SP5GW/Crystal_Radio_Receiver/img/ReceiverPhotos/IMG_1018_radio_internal.jpg

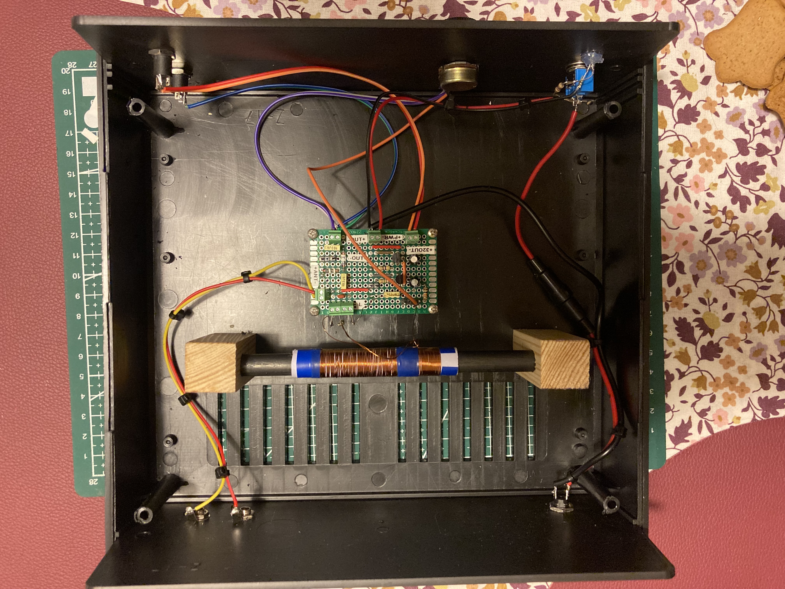
img/ReceiverPhotos/IMG_1018_radio_internal.jpg
