SP5GW/Crystal_Radio_Receiver/img/SolecKujawskiSite/SolecKujawski_2.jpg

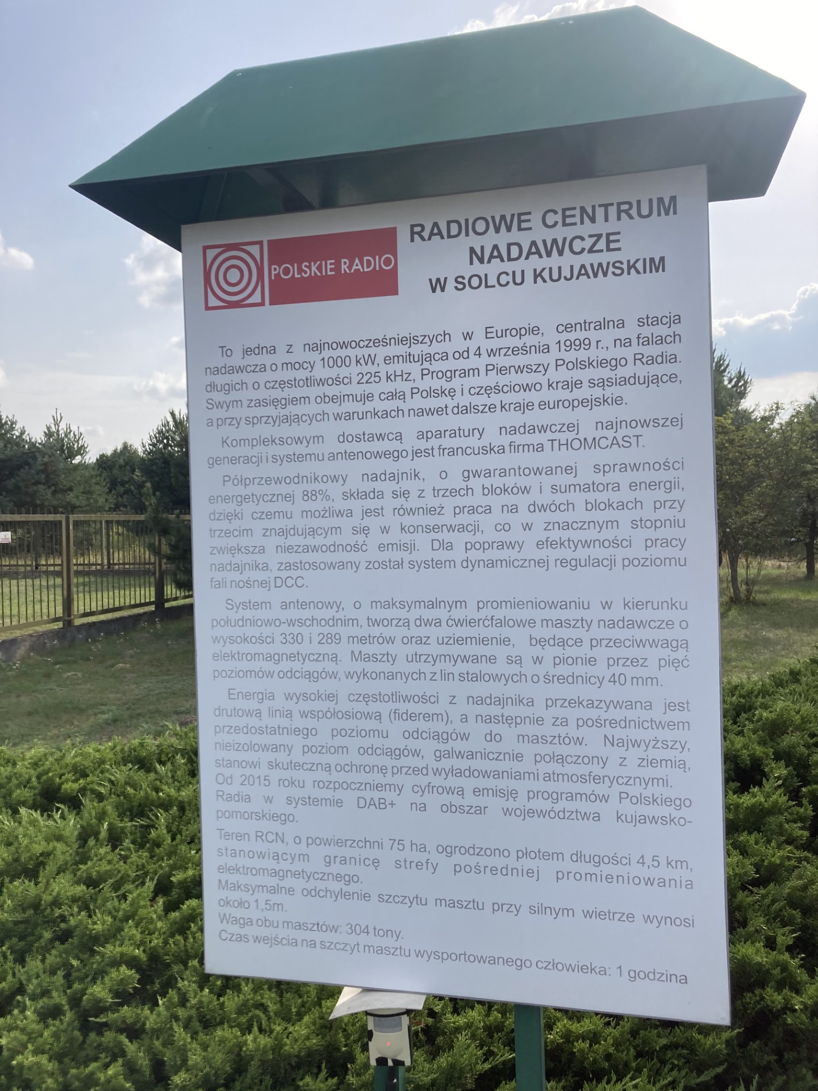
img/SolecKujawskiSite/SolecKujawski_2.jpg
