SP5GW/Crystal_Radio_Receiver/meas/power_supply_filter/0_Unfiltered_signal.png

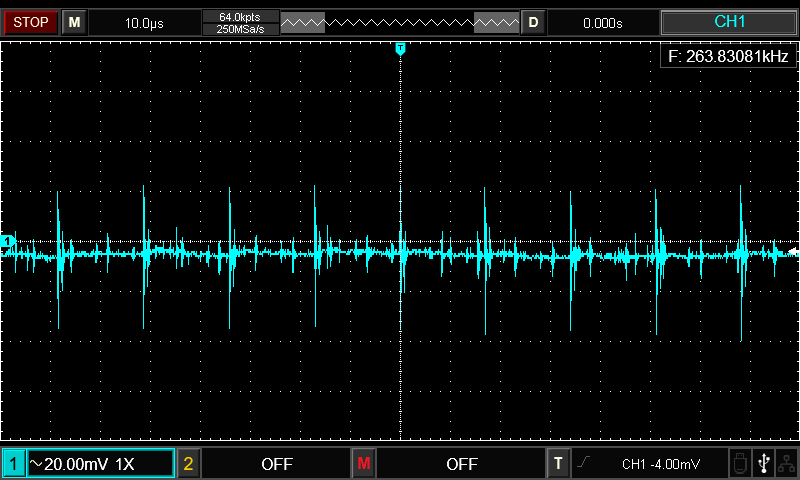
meas/power_supply_filter/0_Unfiltered_signal.png
