SP5GW/Crystal_Radio_Receiver/meas/power_supply_filter/1_C1_cap_added.png

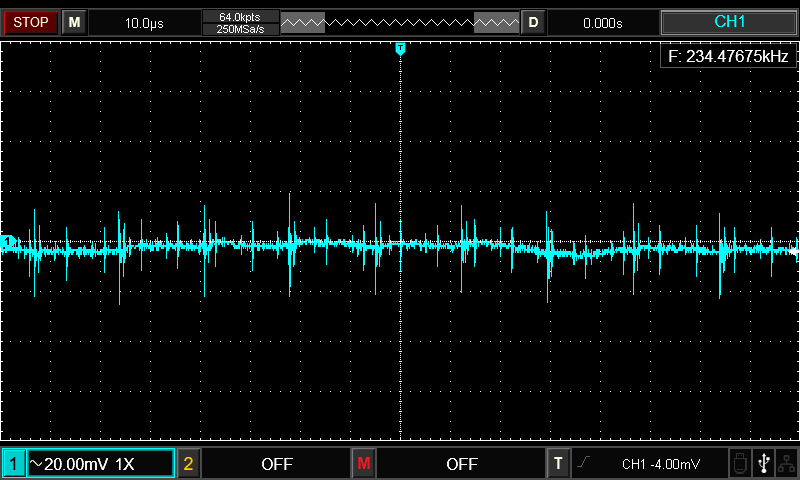
meas/power_supply_filter/1_C1_cap_added.png
