SP5GW/Crystal_Radio_Receiver/meas/power_supply_filter/2__C1_cap_and_L1_added.png

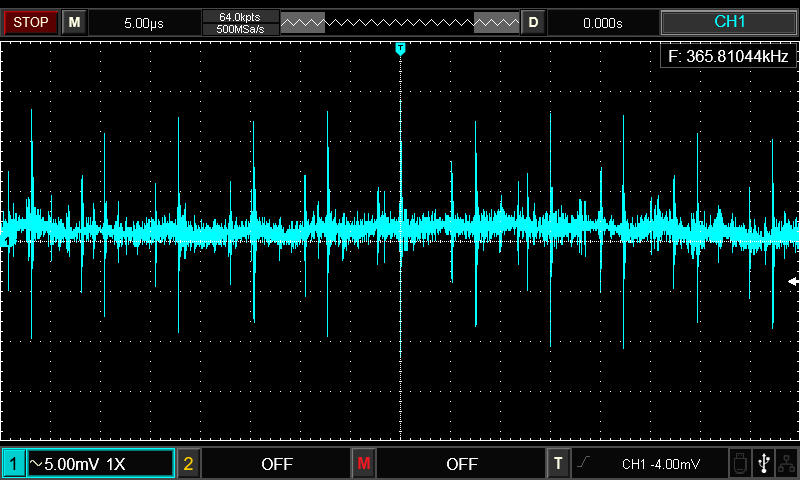
meas/power_supply_filter/2__C1_cap_and_L1_added.png
