SP5GW/Crystal_Radio_Receiver/meas/power_supply_filter/5__C1_cap_and_L1_C2_C3_L2_reg_added.png

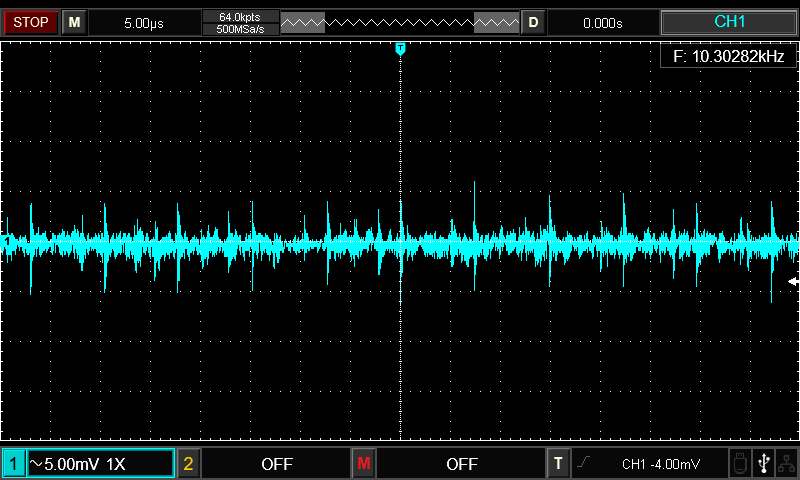
meas/power_supply_filter/5__C1_cap_and_L1_C2_C3_L2_reg_added.png
