SP5GW/Crystal_Radio_Receiver/sim/BandpassFilterStage_Circuit_Ant_Res.png

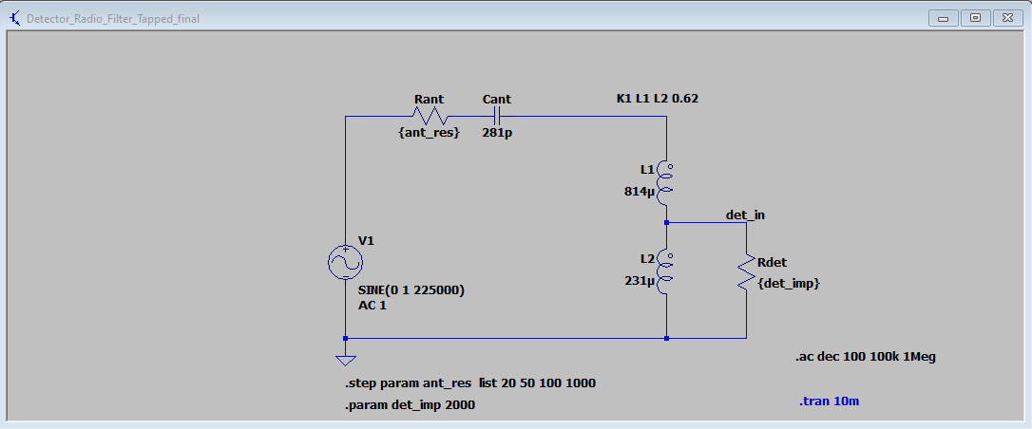
sim/BandpassFilterStage_Circuit_Ant_Res.png
