SP5GW/Crystal_Radio_Receiver/sim/BandpassFilterStage_Circuit_Cap_Add.png

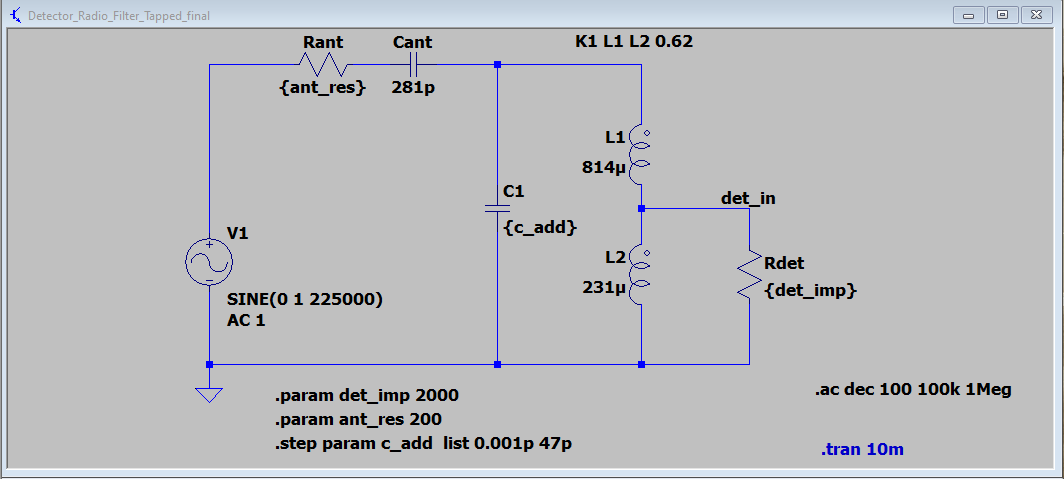
sim/BandpassFilterStage_Circuit_Cap_Add.png
