SP5GW/Crystal_Radio_Receiver/sim/BandpassFilterStage_Circuit_Det_Res.png

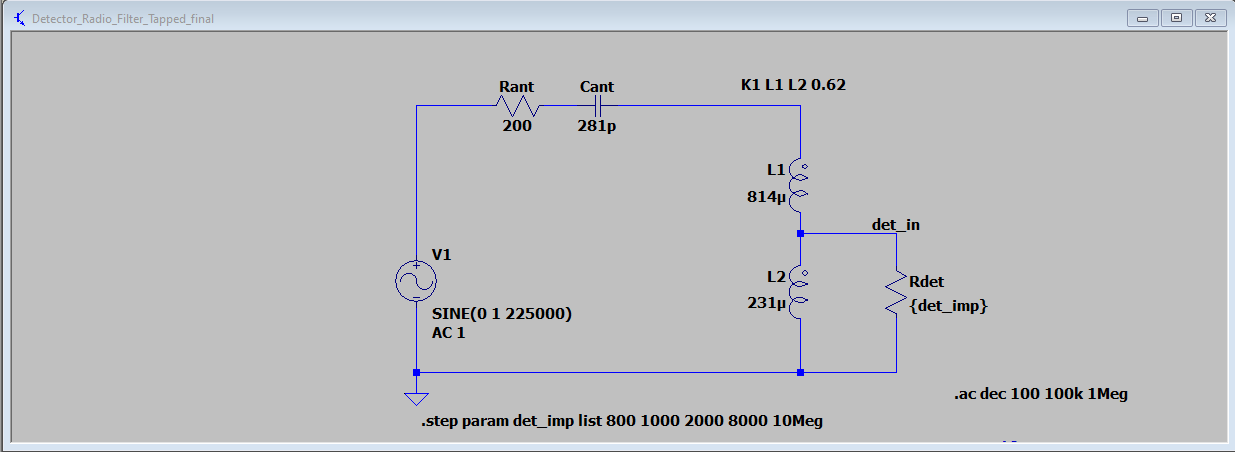
sim/BandpassFilterStage_Circuit_Det_Res.png
