SP5GW/Crystal_Radio_Receiver/sim/BandpassFilterStage_FrequencyResponse_Cap_Add.png

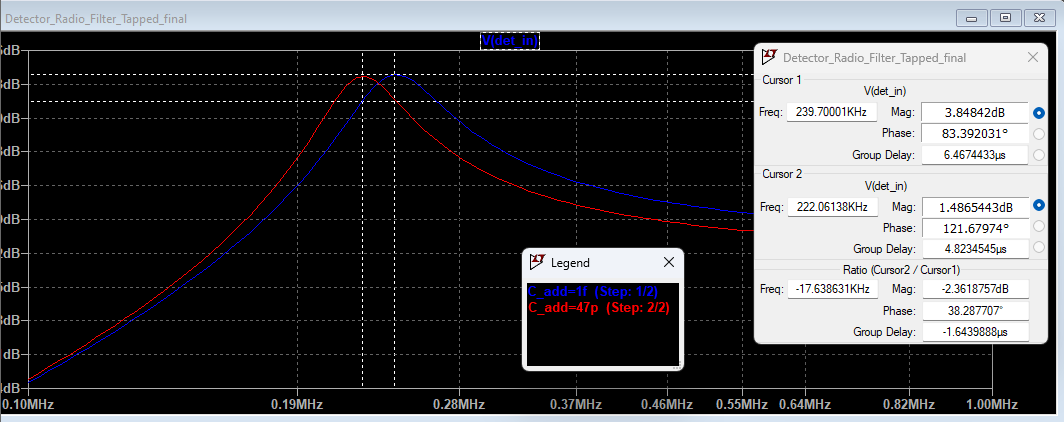
sim/BandpassFilterStage_FrequencyResponse_Cap_Add.png
