SP5GW/Crystal_Radio_Receiver/sim/BandpassFilterStage_FrequencyResponse_Det_Res.png

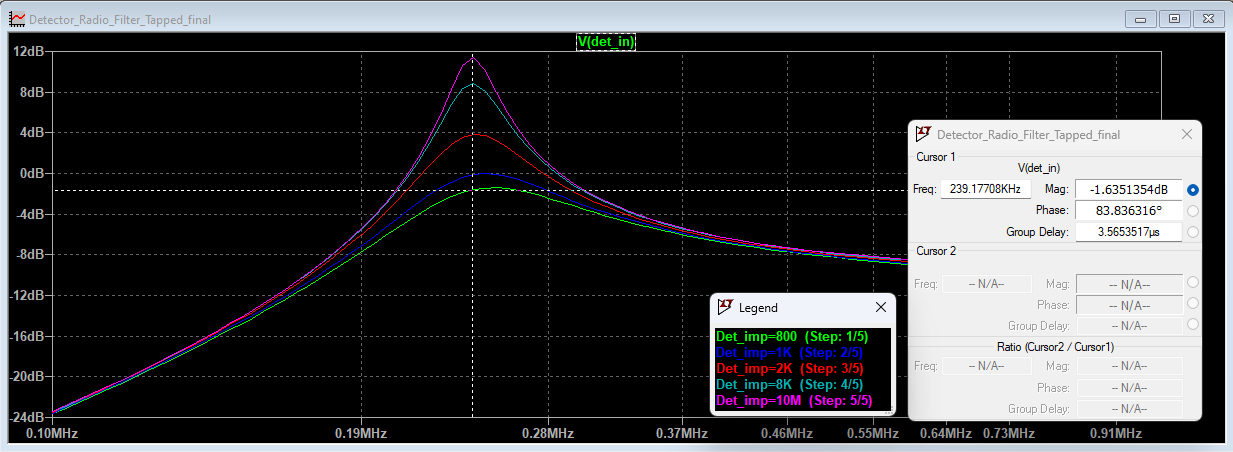
sim/BandpassFilterStage_FrequencyResponse_Det_Res.png
