SP5GW/Crystal_Radio_Receiver/sim/Detector_Radio_Complete_final.asc

B1: bv; V=V(Carrier)*V(Baseband)
C1: cap; 10n
C2: cap; 10n
C3: cap; 47p
C4: cap; 10µ
C5: polcap; 10µ; V=16 Irms=413m Rser=0.22 Lser=0 mfg="Chemi-Con" pn="LXF16VB181M6X15LL" type="Al electrolytic"
C6: cap; 10n
Cant: cap; 281p
D1: schottky; 1N34A
D2: schottky; 1N34A
L1: ind2; 231µ
L2: ind2; 814µ
Pot1: res; 150k
Pot2: res; 50k
Q1: npn; BC547B
Q2: pnp; BC557B
R2: res; 6.8Meg
R3: res; 47
R4: res; 4000
R5: res; 10k
Rantsysloss: res; 200
V1: signal; SINE(0 1 225K)
V2: signal; SINE(0.1 0.08 1K)
V4: voltage; 12V
Named nets: 0, Carrier, Baseband, LCout, DetOut, AmpOut, AntOut
.ac dec 100 100k 1Meg
.tran 10m
K L1 L2 0.61
