SP5GW/Crystal_Radio_Receiver/sim/Detector_Radio_Filter_Tapped_final.asc

C1: cap; {c_add}
Cant: cap; 281p
L1: ind2; 814µ
L1_a: ind2; 814
L2: ind2; 231µ
L2_a: ind2; 231
L3: ind2; 231
L4: ind2; 814
Leff: ind2; 1.583
R1: res; 20
R2: res; 20
R3: res; 20
R4: res; 2000
R_load: res; 2000
Rant: res; {ant_res}
Rdet: res; {det_imp}
Rdet_b: res; 13705
Rload_: res; 13705
V1: signal; SINE(0 1 225000); AC 1
V2: signal; SINE(0 1 225000); AC 1
V3: signal; SINE(0 1 225000); AC 1
V4: signal; SINE(0 1 225000); AC 1
Named nets: 0, det_in, det_in_b
.ac dec 100 100k 1Meg
.tran 10m
K1 L1 L2 0.62
.step param det_imp list 800 1000 2000 8000 10Meg
K2 L1_a L2_a 0.62
.param det_imp 2000
Base Circuit
Variant a) using idealized transformer with massive reactances
< === equivalent ===>
k=M/SQRT(L1*L2) => M=k/SQRT(L1*L2)
M=0.62*SQRT(814*231*10^-12)=269uH
 
Lp = L1+L2+2M
Lp=814u+231u+2*269u=1583u
 
fr=1/(2*PI*SQRT(Lp*Cant)
fr=1/(2*3.14*SQRT(1583*281*10^-18))=239kHz
Ls=L2
Ls=231u
 
Lp=1583u
 
N=(Np/Ns)=SQRT(Lp/Ls)
N=SQRT(1583u/231u)=SQRT(6.85)=2.62
 
Rdet_/Rdet_in=N^2 => Rdet_=Rdet_in*N^2
Rdet_=2000*6.85=13705ohm
K3 L3 L4 0.62
.step param ant_res  list 20 50 100 1000
.param ant_res 200
.step param c_add  list 0.001p 47p
