SP5GW/Crystal_Radio_Receiver/sim/Detector_Radio_Transistor_Low_Pass_Filter_final.asc

C1: cap; 10n
R3: res; 10k
V1: signal; SINE(); AC 0.017
Named nets: 0, Vin, Vout
.ac dec 100 0.1k 20k
