SP5GW/Crystal_Radio_Receiver/docs/Detector_Radio_With_Optional_Amp.kicad_sch

## KiCad design docs/Detector_Radio_With_Optional_Amp.kicad_sch (2024-01-07)

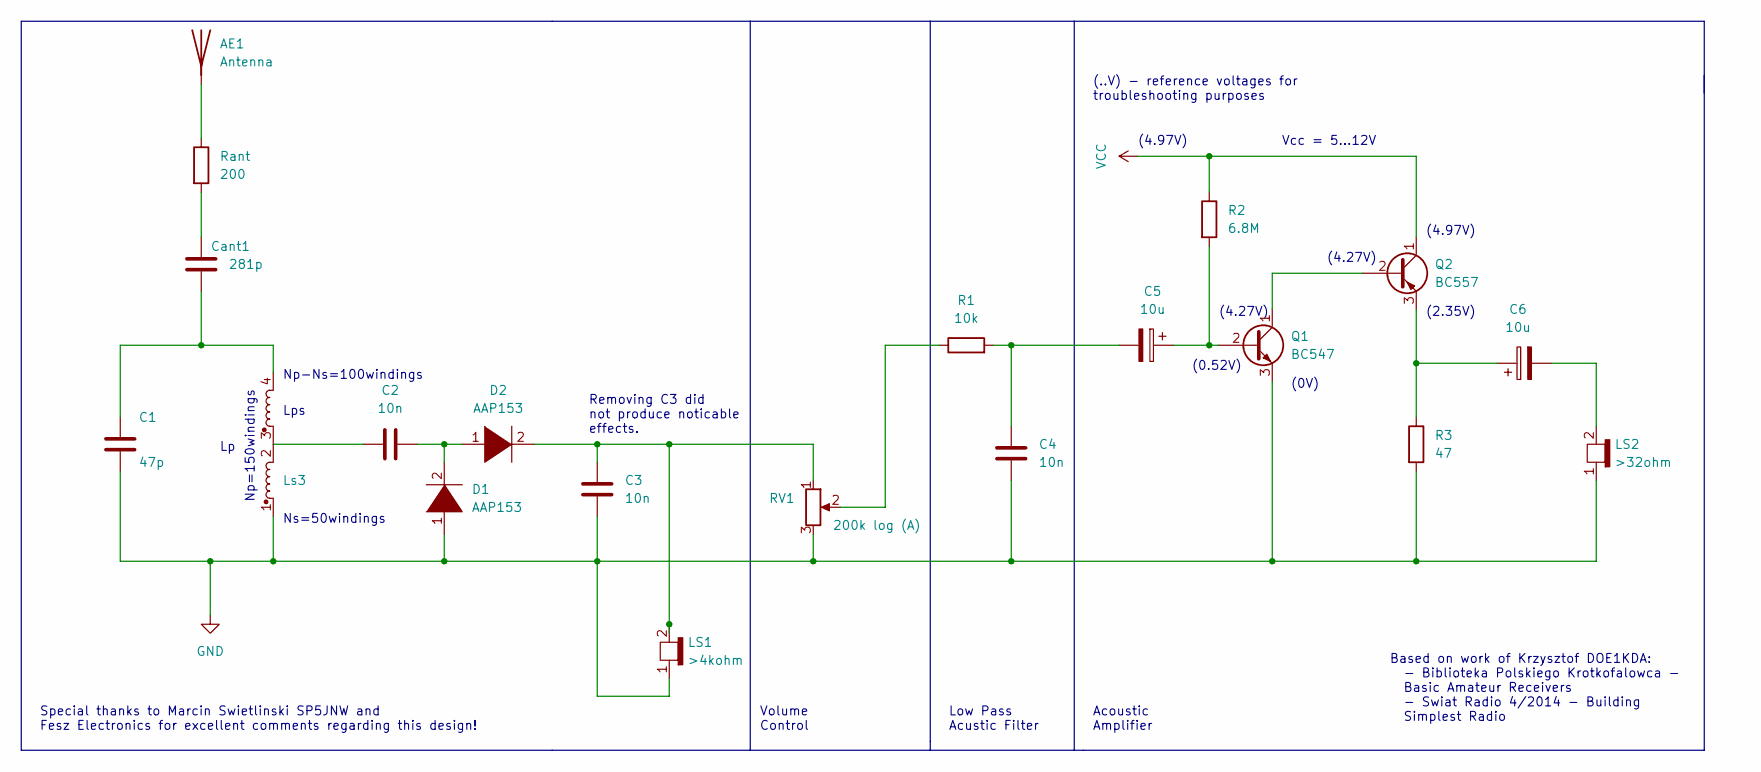
[picture p59: schematic Detector_Radio_With_Optional_Amp.kicad_sch]

Parts:
AE1: Antenna
C1: 47p
C2, C3, C4: 10n
C5, C6: 10u
Cant1: 281p
D1, D2: AAP153
LS1: >4kohm
LS2: >32ohm
Ls3: L_Coupled
Q1: BC547; TO-92_Inline
Q2: BC557; TO-92_Inline
R1: 10k
R2: 6.8M
R3: 47
RV1: 200k log (A)
Rant: 200

Connections:
GND: C1.2, C3.2, C4.2, D1.1 (K), LS1.1 (-), LS2.1 (-), Ls3.1, Q1.3 (E), R3.2, RV1.3
unnamed: AE1.1, Rant.1
unnamed: C1.1, Cant1.2, Ls3.4
unnamed: C2.1, Ls3.2, Ls3.3
unnamed: C2.2, D1.2 (A), D2.1 (K)
unnamed: C3.1, D2.2 (A), LS1.2 (+), RV1.1
unnamed: C4.1, C5.2, R1.2
unnamed: C5.1, Q1.2 (B), R2.2
unnamed: C6.1, Q2.3 (E), R3.1
unnamed: C6.2, LS2.2 (+)
unnamed: Cant1.1, Rant.2
unnamed: Q1.1 (C), Q2.2 (B)
unnamed: R1.1, RV1.2
VCC: Q2.1 (C), R2.1

Notes on the sheet:
(..V) - reference voltages for troubleshooting purposes
Np-Ns=100windings
(4.97V)
Low Pass Acustic Filter
(2.35V)
Ns=50windings
Np=150windings
Lps
(4.27V)
Acoustic Amplifier
Special thanks to Marcin Swietlinski SP5JNW and Fesz Electronics for excellent comments regarding this design!
Volume Control
(0.52V)
Vcc = 5...12V
Based on work of Krzysztof DOE1KDA: - Biblioteka Polskiego Krotkofalowca - Basic Amateur Receivers - Swiat Radio 4/2014 - Building Simplest Radio
(0V)
Removing C3 did not produce noticable effects.
